GeekyDeaks/g29-load-cell/scad/top.scad

use <plunger.scad>;
top();
